AngularSpecter/RocketPack/Firmware/sensor tag/Source/uart.h

#include <ioCC2541.h>
#include <hal_defs.h>
#include <hal_board_cfg.h>

#define ENABLE_RX()       st( U0CSR |= BV(6););
#define DISABLE_RX()      st( U0CSR &= ~BV(6););


void UART_init(void);
void calcBAUD(unsigned int baud, unsigned char *M, unsigned char *E);
void repeatBytes(uint8 byte, uint8 count);
void flush_data(uint8* txbuffer);
void flush_byte(uint8* txbuffer);
void sendByte(uint8* txbuffer);
void uartSend( char *pucData, unsigned char ucLength);
void uart_send_data(uint16 *buffer, uint8 len);
